MUTEtheCyberwolf/VALVE-INDEX-DEV-Frunk-1.0/3D Print Files 3mf/EyetrackVRDemoVIDEVFrunk1.3mf

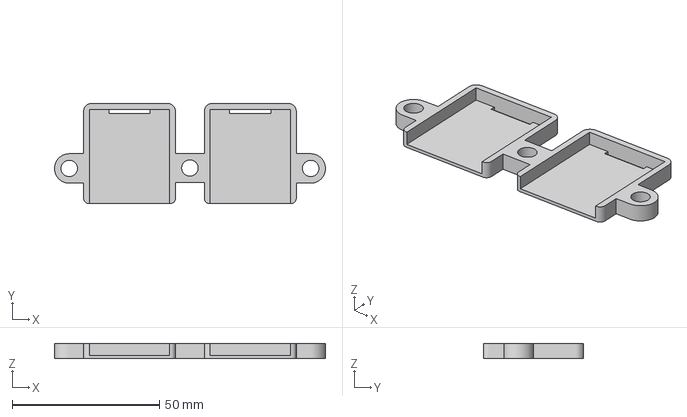
[picture p15: CAD file, 2022-12-26]
3D Print Files 3mf/EyetrackVRDemoVIDEVFrunk1.3mf
92.0 x 34.0 x 5.00 mm
