MUTEtheCyberwolf/VALVE-INDEX-DEV-Frunk-1.0/3D Print Files STL(Ascii)/XIAO Retention Clip for V4 PCB No Letters.stl

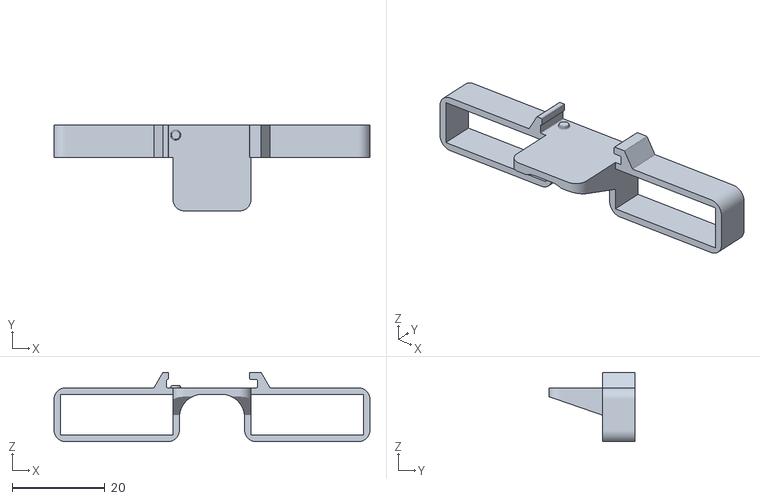
[picture p16: CAD file, 2023-08-11]
3D Print Files STL(Ascii)/XIAO Retention Clip for V4 PCB No Letters.stl
68.0 x 18.5 x 14.9
