MUTEtheCyberwolf/VALVE-INDEX-DEV-Frunk-1.0/3D Print Files 3mf/ValveIndexDEVFrunk1.3mf

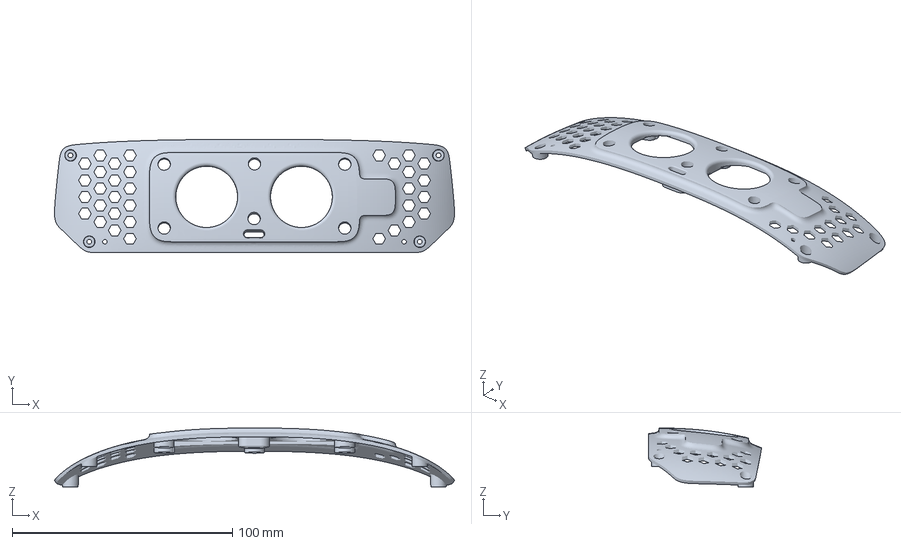
[picture p17: CAD file, 2022-12-26]
3D Print Files 3mf/ValveIndexDEVFrunk1.3mf
181.5 x 51.3 x 26.8 mm
