MUTEtheCyberwolf/VALVE-INDEX-DEV-Frunk-1.0/3D Print Files 3mf/FacialTrackerBeerHingeVIDEVFrunk1.3mf

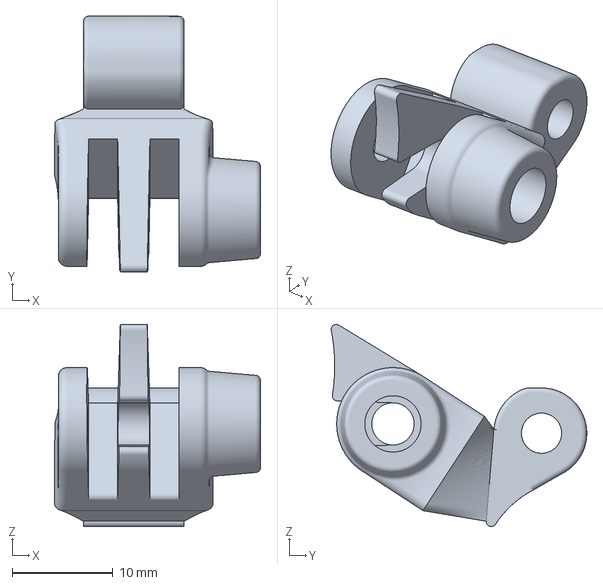
[picture p19: CAD file, 2022-12-26]
3D Print Files 3mf/FacialTrackerBeerHingeVIDEVFrunk1.3mf
20.5 x 25.4 x 20.1 mm
